supermoun62/Projet_DHT22-et-LCD/Liste_Materiel_Affichage_DHT22/Liste_Materiel_Affichage_Temp_Humidite.pdf

Liste_Materiel_Affichage_Temp_Humidite.pdf | 1 sur 1
Q | | | TME-EU | cPix.fr | Gotronic | Conrad | Lextronic
1 | J1 | Connecteur 1*3 | MKDSN 2,5/ 3-5,08 1888690 (https://www.tme.eu/fr/details/mkdsn2.5_3-5.08/borniers-de-serrage-pcb/phoenix-contact/mkdsn-2-5-3-5-08-1888690/)
1 | F1 | Support fusible | ZHL77
| | Capot | ZHL7X-H (https://www.tme.eu/fr/katalog/?search=zhl77&s_field=1000011&s_order=desc)
1 | F1 | 100ma
1 | TR1 | 220v – 12v 100ma | BV EI 302 2938 (https://www.tme.eu/fr/details/bvei3022938/transformateurs-pour-pcb/hahn/bv-ei-302-2938/)
1 | D1 | Pont de diode | NTE5304 (https://www.tme.eu/fr/katalog/?search=B40C1500g&s_field=1000011&s_order=desc)
1 | C1 | 2200uf-25v | KM2200/25 (https://www.tme.eu/fr/katalog/?search=km2200%2F25&s_field=1000011&s_order=desc)
1 | C2 | 330nf | BFC233820334 (https://www.tme.eu/fr/katalog/?search=BFC233820334&s_field=1000011&s_order=desc)
1 | U1 | Régulateur 9v | NTE1910 (https://www.tme.eu/fr/katalog/?search=NTE1910&s_field=1000011&s_order=desc)
1 | | Refroidisseur | FK210SACB (https://www.tme.eu/fr/katalog/?search=FK210SA&s_field=1000011&s_order=desc)
| | Pâte thermique
2 | C3, C4 | 100nf | CCK-100N (https://www.tme.eu/fr/details/cck-100n/condensateurs-ceramiques-tht/sr-passives/#)
1 | R1 | 820 -1 % | MBB02070C8200FCT00 (https://www.tme.eu/fr/details/mbb02070c8200fct00/resistances-metallisees-tht-0-6w/vishay/)
1 | D2 | Diode rouge
1 | D3 | 1N4007
3 | R2, R3, R4 | 4k7-1 % | MBB02070C4701FCT00 (https://www.tme.eu/fr/details/mbb02070c4701fct00/resistances-metallisees-tht-0-6w/vishay/)
2 | J2, J3 | Connecteur Pin - 4 | 1-826629-16 (https://www.tme.eu/fr/katalog/?search=1-826629&s_field=1000011&s_order=desc)
1 | | Arduino nano | | | 25952
2 | | Connecteur Pin – 15
1 | | LCD 2*16 | | | 34940
1 | | DHT22
1 | | Adhésif thermique | | JJIJCOYNA
1 | | Presse-Etoupe Donau Elektronik 527190 | | | | 527190 (https://www.conrad.fr/fr/p/presse-etoupe-donau-elektronik-527190-avec-decharge-de-traction-m10-polyamide-noir-1-pc-s-527190.html)
