supermoun62/Projet_DHT22-et-LCD/Doc_Tech_Affichage_DHT22/Stelvio_cover.pdf

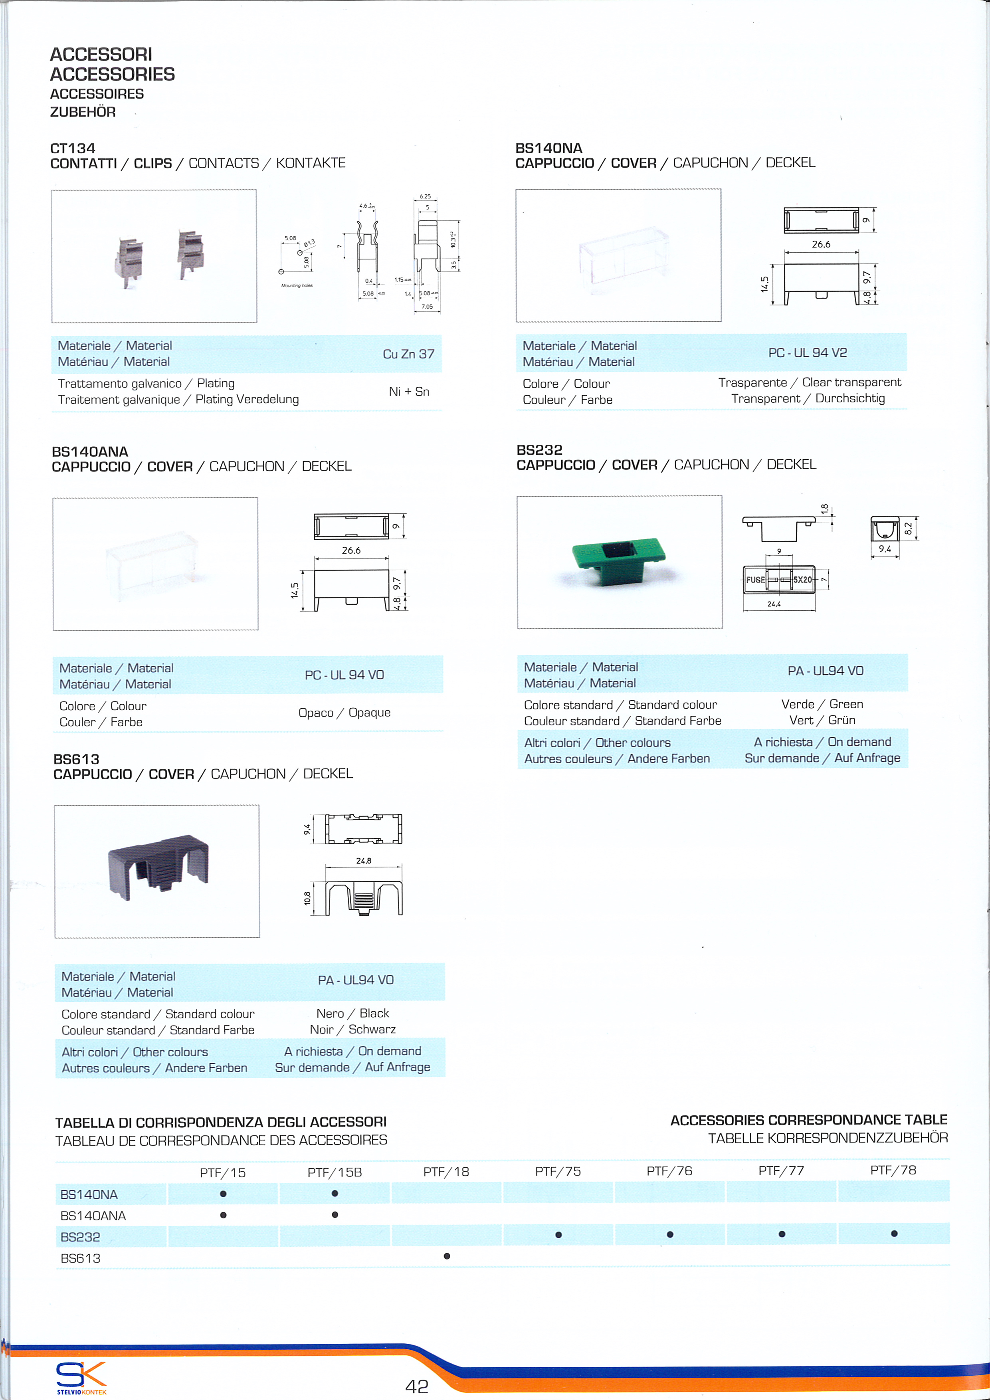
[picture p12: page 1]
