supermoun62/Projet_DHT22-et-LCD/Schema_Affichage_DHT22/Affichage_Temp_Humidite.pdf

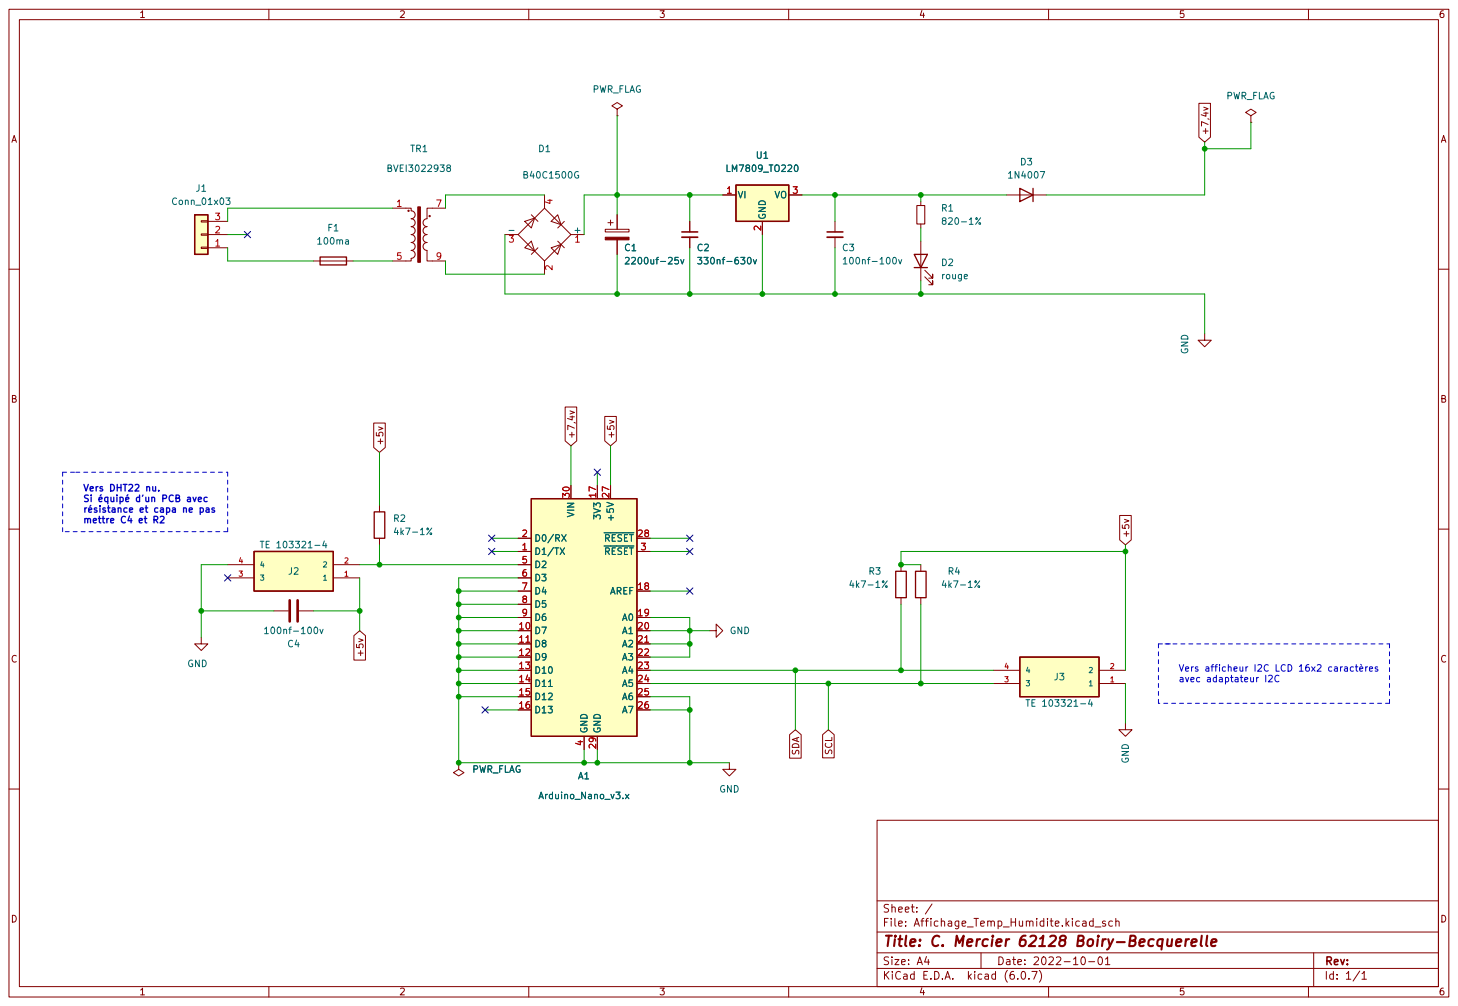
[picture p19: page 1]

2 VO 3 PWR_FLAG A1 Arduino_Nano_v3.x D1/TX 1 D7 10 D8 11 D9 12 D10 13 D11 14 D12 15 D13 16 3V3 17 AREF 18 A0 19 D0/RX 2 A1 20 A2 21 A3 22 A4 23 A5 24 A6 25 A7 26 +5V 27

File: Affichage_Temp_Humidite.kicad_sch Sheet: /
Id: 1/1 Title: C. Mercier 62128 Boiry-Becquerelle
