supermoun62/Projet_DHT22-et-LCD/PCB_PDF_Affichage_DHT22/Affichage_Temp_Humidite-B_Cu.pdf

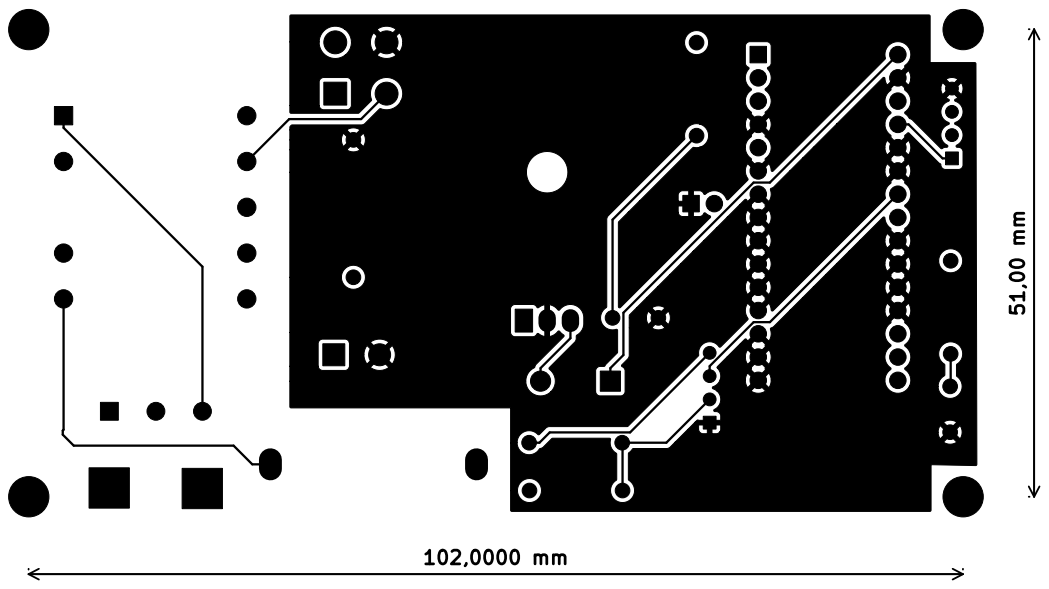
[picture p20: page 1]
