supermoun62/Projet_DHT22-et-LCD/PCB_PDF_Affichage_DHT22/Affichage_Temp_Humidite-F_Courtyard.pdf

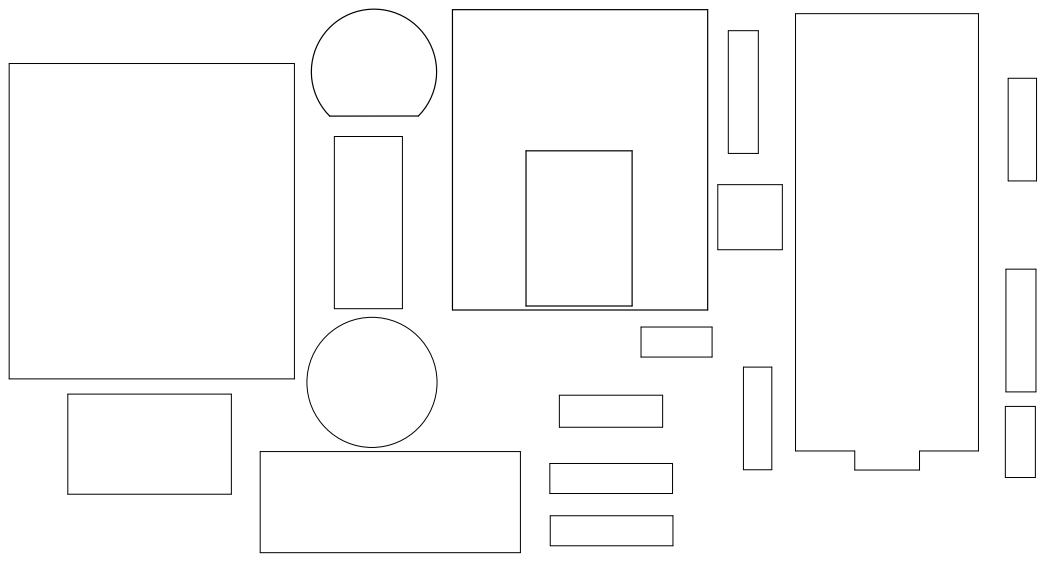
[picture p22: page 1]
