supermoun62/Projet_DHT22-et-LCD/PCB_PDF_Affichage_DHT22/Affichage_Temp_Humidite-F_Fab.pdf

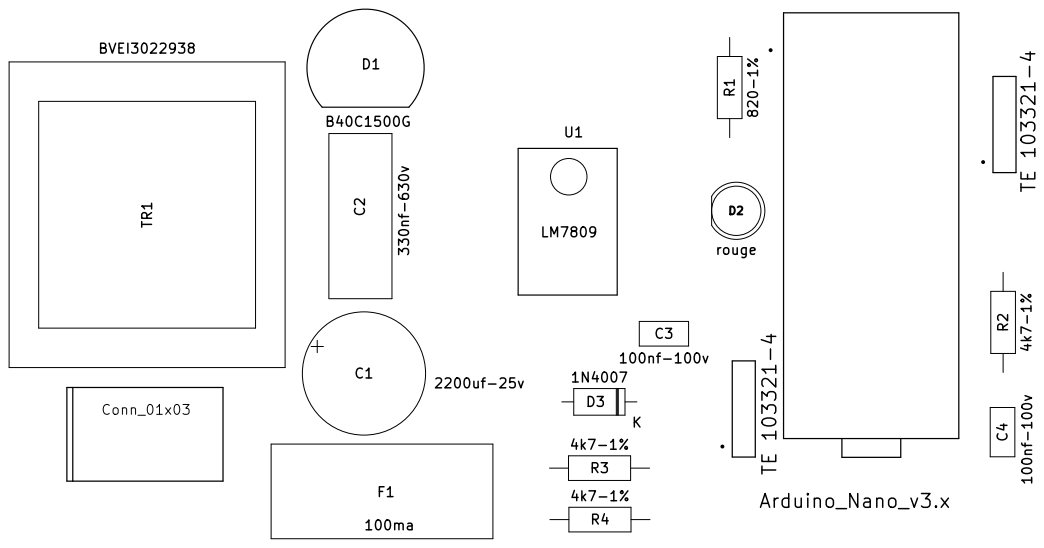
[picture p24: page 1]
